acolangelo/flight-control/3D/objects/usb-type-b-panel-mount/USB_Type_B_01.jpg

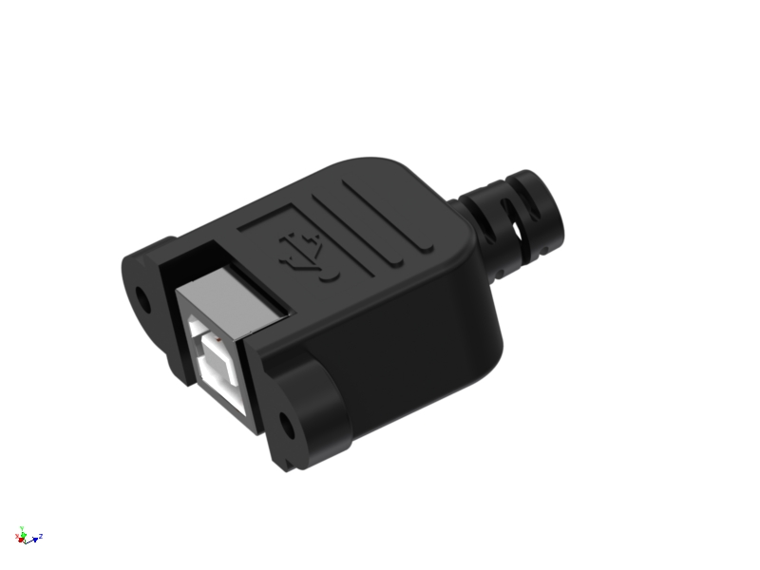
3D/objects/usb-type-b-panel-mount/USB_Type_B_01.jpg
