acolangelo/flight-control/3D/renders/back-panel-cut-out.png

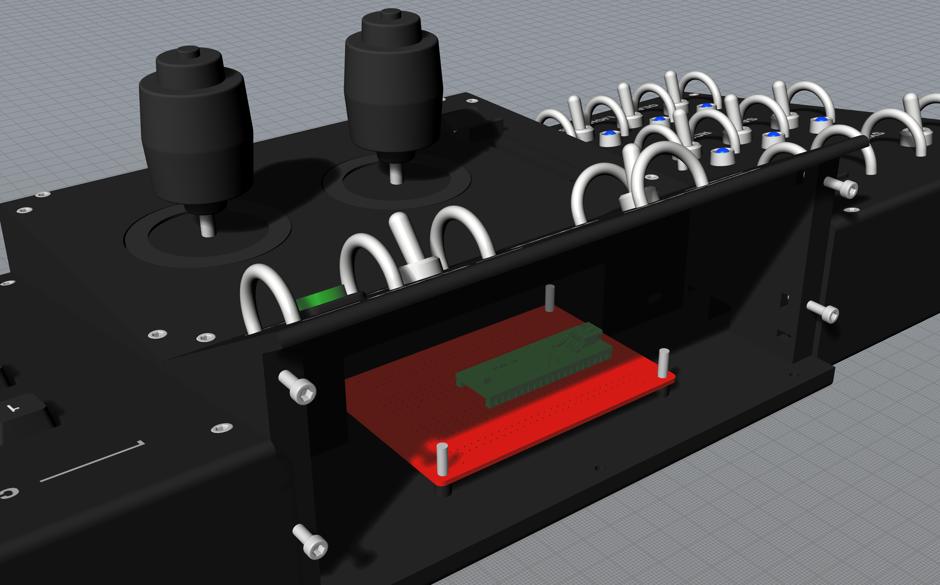
3D/renders/back-panel-cut-out.png
