acolangelo/flight-control/3D/renders/back-panel.jpg

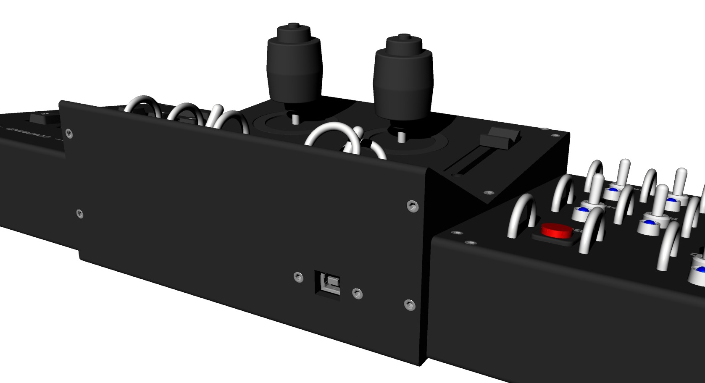
3D/renders/back-panel.jpg
