acolangelo/flight-control/3D/renders/exploded.jpg

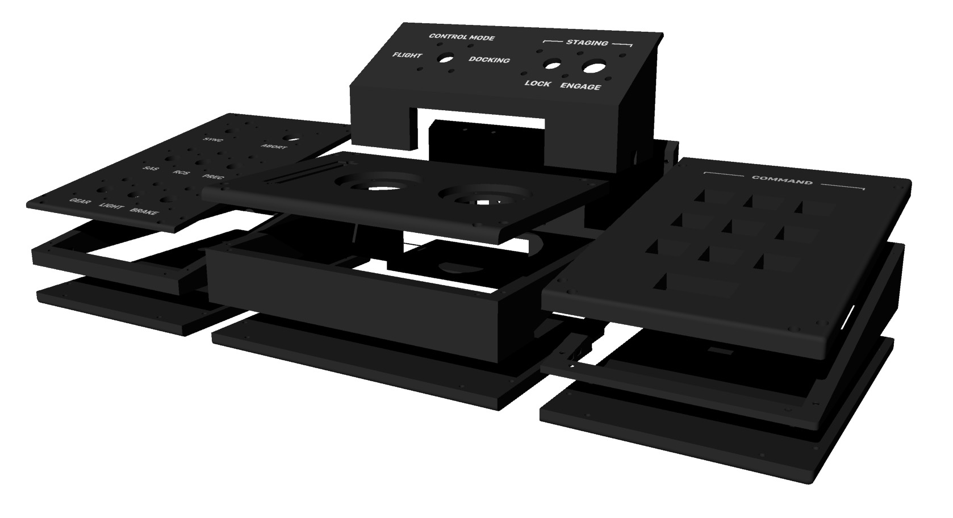
3D/renders/exploded.jpg
