acolangelo/flight-control/3D/renders/full.jpg

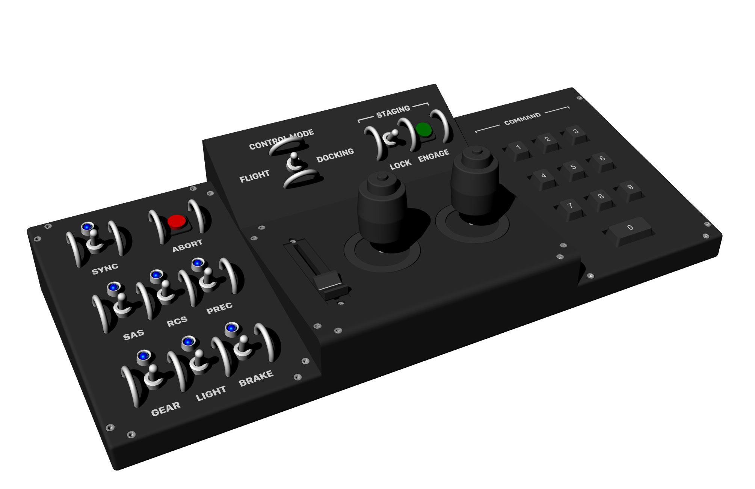
3D/renders/full.jpg
