acolangelo/flight-control/3D/print/right-top.stl

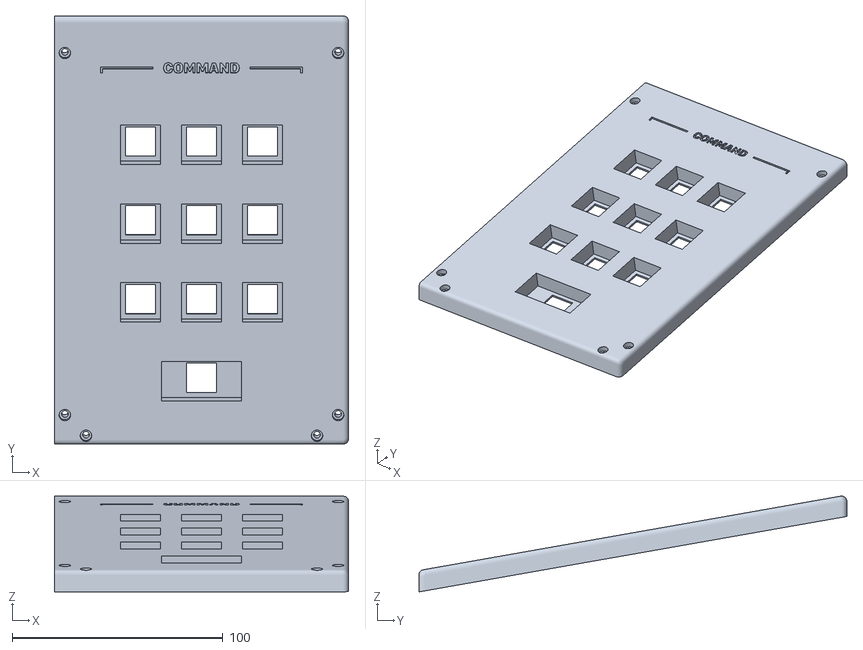
[picture p27: CAD file, 2017-07-27]
3D/print/right-top.stl
139.7 x 203.2 x 45.5
